Cristiaangz/Smart-Clamp/SmartClamp/ESP32/circuit schematic/v0.14.png

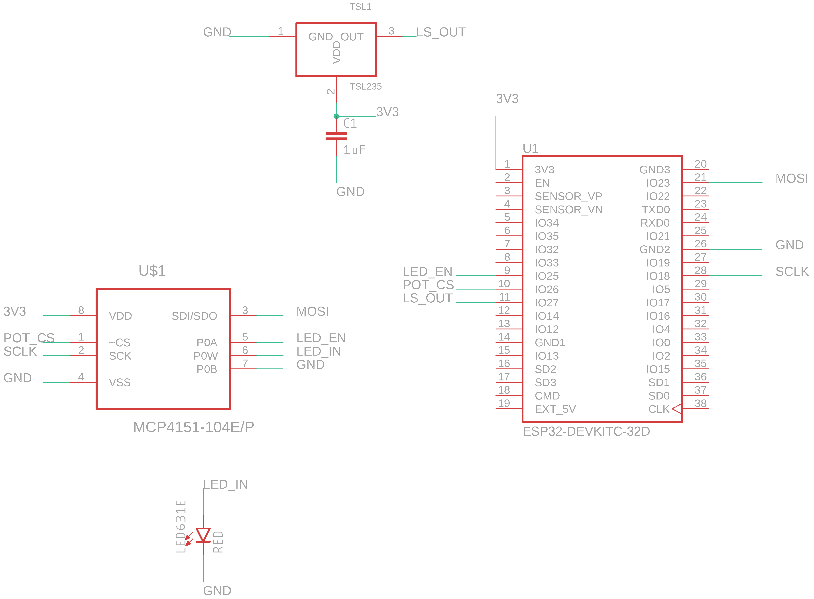
SmartClamp/ESP32/circuit schematic/v0.14.png
