Cristiaangz/Smart-Clamp/Tests/Initial Tests/Integrated Light and Motion Tests/30%Mid1.csv

Time [s] | Intensity A | Laser On | AcX | AcY | AcZ | GyX | GyY | GyZ | MPU Temp [C]
0.0 | 16.666666666666700 | TRUE | 0 | 0 | 0 | 0 | 0 | 0 | 25.352941176470600
0.10 | 500.0 | TRUE | 0 | 0 | 0 | 0 | 0 | 0 | 25.352941176470600
0.20 | 2200.0 | TRUE | 0 | 0 | 0 | 0 | 0 | 0 | 25.352941176470600
0.30 | 2200.0 | TRUE | 0 | 0 | 0 | 0 | 0 | 0 | 25.352941176470600
0.40 | 2183.3333333333300 | TRUE | 0 | 0 | 0 | 0 | 0 | 0 | 25.352941176470600
0.50 | 2200.0 | TRUE | 0 | 0 | 0 | 0 | 0 | 0 | 25.352941176470600
0.60 | 2200.0 | TRUE | 0 | 0 | 0 | 0 | 0 | 0 | 25.352941176470600
0.70 | 2183.3333333333300 | TRUE | 0 | 0 | 0 | 0 | 0 | 0 | 25.352941176470600
0.80 | 2200.0 | TRUE | 0 | 0 | 0 | 0 | 0 | 0 | 25.352941176470600
0.90 | 2200.0 | TRUE | 0 | 0 | 0 | 0 | 0 | 0 | 25.352941176470600
0.100 | 2200.0 | TRUE | 0 | 0 | 0 | 0 | 0 | 0 | 25.352941176470600
0.110 | 2183.3333333333300 | TRUE | 0 | 0 | 0 | 0 | 0 | 0 | 25.352941176470600
0.120 | 2200.0 | TRUE | 0 | 0 | 0 | 0 | 0 | 0 | 25.352941176470600
0.130 | 2200.0 | TRUE | 0 | 0 | 0 | 0 | 0 | 0 | 25.352941176470600
0.140 | 2183.3333333333300 | TRUE | 0 | 0 | 0 | 0 | 0 | 0 | 25.352941176470600
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
