Cristiaangz/Smart-Clamp/Tests/Initial Tests/Integrated Light and Motion Tests/30%Mid2.csv

Time [s] | Intensity A | Laser On | AcX | AcY | AcZ | GyX | GyY | GyZ | MPU Temp [C]
0.0 | 16.666666666666700 | TRUE | 0 | 0 | 0 | 0 | 0 | 0 | 25.541176470588200
0.10 | 433.3333333333330 | TRUE | 0 | 0 | 0 | 0 | 0 | 0 | 25.541176470588200
0.20 | 2183.3333333333300 | TRUE | 0 | 0 | 0 | 0 | 0 | 0 | 25.541176470588200
0.30 | 2200.0 | TRUE | 0 | 0 | 0 | 0 | 0 | 0 | 25.541176470588200
0.40 | 2183.3333333333300 | TRUE | 0 | 0 | 0 | 0 | 0 | 0 | 25.541176470588200
0.50 | 2200.0 | TRUE | 0 | 0 | 0 | 0 | 0 | 0 | 25.541176470588200
0.60 | 2200.0 | TRUE | 0 | 0 | 0 | 0 | 0 | 0 | 25.541176470588200
0.70 | 2183.3333333333300 | TRUE | 0 | 0 | 0 | 0 | 0 | 0 | 25.541176470588200
0.80 | 2200.0 | TRUE | 0 | 0 | 0 | 0 | 0 | 0 | 25.541176470588200
0.90 | 2200.0 | TRUE | 0 | 0 | 0 | 0 | 0 | 0 | 25.541176470588200
0.100 | 2183.3333333333300 | TRUE | 0 | 0 | 0 | 0 | 0 | 0 | 25.541176470588200
0.110 | 2200.0 | TRUE | 0 | 0 | 0 | 0 | 0 | 0 | 25.541176470588200
0.120 | 2183.3333333333300 | TRUE | 0 | 0 | 0 | 0 | 0 | 0 | 25.541176470588200
0.130 | 2200.0 | TRUE | 0 | 0 | 0 | 0 | 0 | 0 | 25.541176470588200
0.140 | 2200.0 | TRUE | 0 | 0 | 0 | 0 | 0 | 0 | 25.541176470588200
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
