Cristiaangz/Smart-Clamp/Tests/Initial Tests/Integrated Light and Motion Tests/30%Static1.csv

Time [s] | Intensity A | Laser On | AcX | AcY | AcZ | GyX | GyY | GyZ | MPU Temp [C]
0.0 | 16.666666666666700 | TRUE | 0 | 0 | 0 | 0 | 0 | 0 | 24.929411764705900
0.10 | 416.6666666666670 | TRUE | 0 | 0 | 0 | 0 | 0 | 0 | 24.929411764705900
0.20 | 2166.6666666666700 | TRUE | 0 | 0 | 0 | 0 | 0 | 0 | 24.929411764705900
0.30 | 2166.6666666666700 | TRUE | 0 | 0 | 0 | 0 | 0 | 0 | 24.929411764705900
0.40 | 2166.6666666666700 | TRUE | 0 | 0 | 0 | 0 | 0 | 0 | 24.929411764705900
0.50 | 2166.6666666666700 | TRUE | 0 | 0 | 0 | 0 | 0 | 0 | 24.929411764705900
0.60 | 2183.3333333333300 | TRUE | 0 | 0 | 0 | 0 | 0 | 0 | 24.929411764705900
0.70 | 2150.0 | TRUE | 0 | 0 | 0 | 0 | 0 | 0 | 24.929411764705900
0.80 | 2166.6666666666700 | TRUE | 0 | 0 | 0 | 0 | 0 | 0 | 24.929411764705900
0.90 | 2166.6666666666700 | TRUE | 0 | 0 | 0 | 0 | 0 | 0 | 24.929411764705900
0.100 | 2166.6666666666700 | TRUE | 0 | 0 | 0 | 0 | 0 | 0 | 24.929411764705900
0.110 | 2166.6666666666700 | TRUE | 0 | 0 | 0 | 0 | 0 | 0 | 24.929411764705900
0.120 | 2166.6666666666700 | TRUE | 0 | 0 | 0 | 0 | 0 | 0 | 24.929411764705900
0.130 | 2183.3333333333300 | TRUE | 0 | 0 | 0 | 0 | 0 | 0 | 24.929411764705900
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
