Cristiaangz/Smart-Clamp/Tests/Initial Tests/Integrated Light and Motion Tests/30%Static2.csv

Time [s] | Intensity A | Laser On | AcX | AcY | AcZ | GyX | GyY | GyZ | MPU Temp [C]
0.0 | 16.666666666666700 | TRUE | 0 | 0 | 0 | 0 | 0 | 0 | 25.16470588235290
0.10 | 666.6666666666670 | TRUE | 0 | 0 | 0 | 0 | 0 | 0 | 25.16470588235290
0.20 | 2166.6666666666700 | TRUE | 0 | 0 | 0 | 0 | 0 | 0 | 25.16470588235290
0.30 | 2183.3333333333300 | TRUE | 0 | 0 | 0 | 0 | 0 | 0 | 25.16470588235290
0.40 | 2150.0 | TRUE | 0 | 0 | 0 | 0 | 0 | 0 | 25.16470588235290
0.50 | 2183.3333333333300 | TRUE | 0 | 0 | 0 | 0 | 0 | 0 | 25.16470588235290
0.60 | 2166.6666666666700 | TRUE | 0 | 0 | 0 | 0 | 0 | 0 | 25.16470588235290
0.70 | 2166.6666666666700 | TRUE | 0 | 0 | 0 | 0 | 0 | 0 | 25.16470588235290
0.80 | 2166.6666666666700 | TRUE | 0 | 0 | 0 | 0 | 0 | 0 | 25.16470588235290
0.90 | 2166.6666666666700 | TRUE | 0 | 0 | 0 | 0 | 0 | 0 | 25.16470588235290
0.100 | 2183.3333333333300 | TRUE | 0 | 0 | 0 | 0 | 0 | 0 | 25.16470588235290
0.110 | 2166.6666666666700 | TRUE | 0 | 0 | 0 | 0 | 0 | 0 | 25.16470588235290
0.120 | 2166.6666666666700 | TRUE | 0 | 0 | 0 | 0 | 0 | 0 | 25.16470588235290
0.130 | 2166.6666666666700 | TRUE | 0 | 0 | 0 | 0 | 0 | 0 | 25.16470588235290
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
