Cristiaangz/Smart-Clamp/Tests/Initial Tests/Gyro/Rotation Tests/10Hz/Graphs/28 RPM/AcX 28 RPM.png

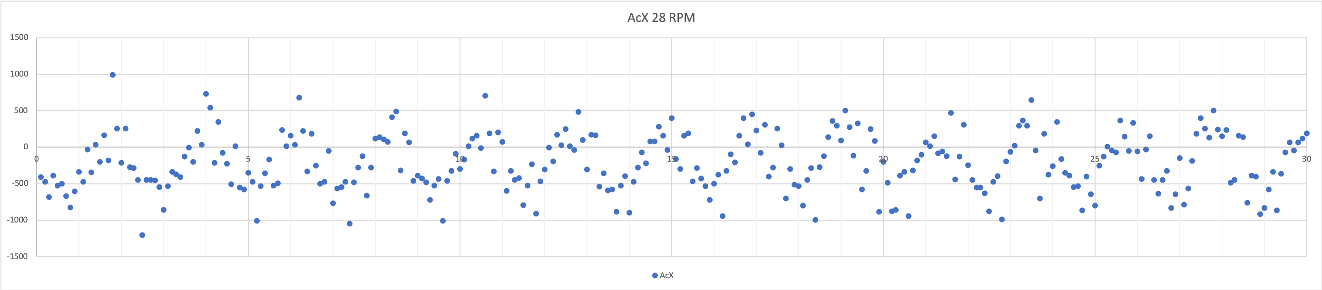
Tests/Initial Tests/Gyro/Rotation Tests/10Hz/Graphs/28 RPM/AcX 28 RPM.png
