Cristiaangz/Smart-Clamp/Tests/Initial Tests/Gyro/Rotation Tests/10Hz/Graphs/28 RPM/AcY 28 RPM.png

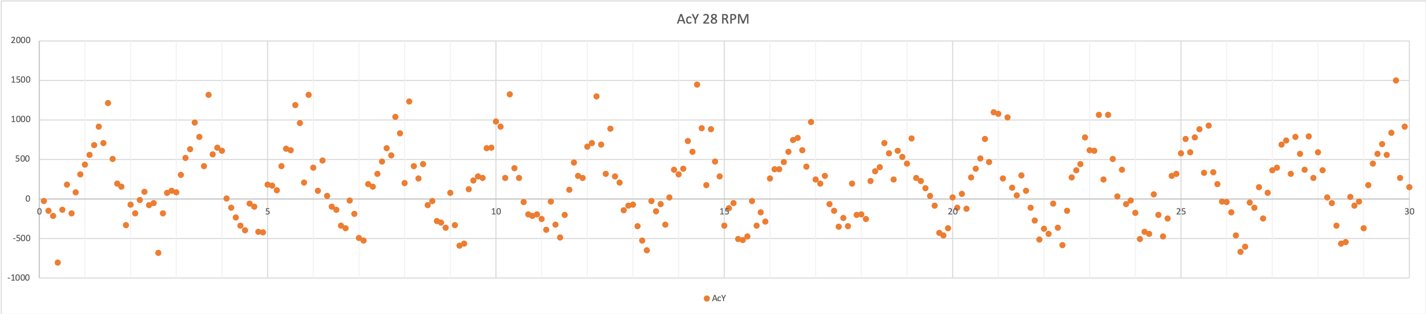
Tests/Initial Tests/Gyro/Rotation Tests/10Hz/Graphs/28 RPM/AcY 28 RPM.png
