Cristiaangz/Smart-Clamp/Tests/Initial Tests/Gyro/Rotation Tests/10Hz/Graphs/80 RPM.png

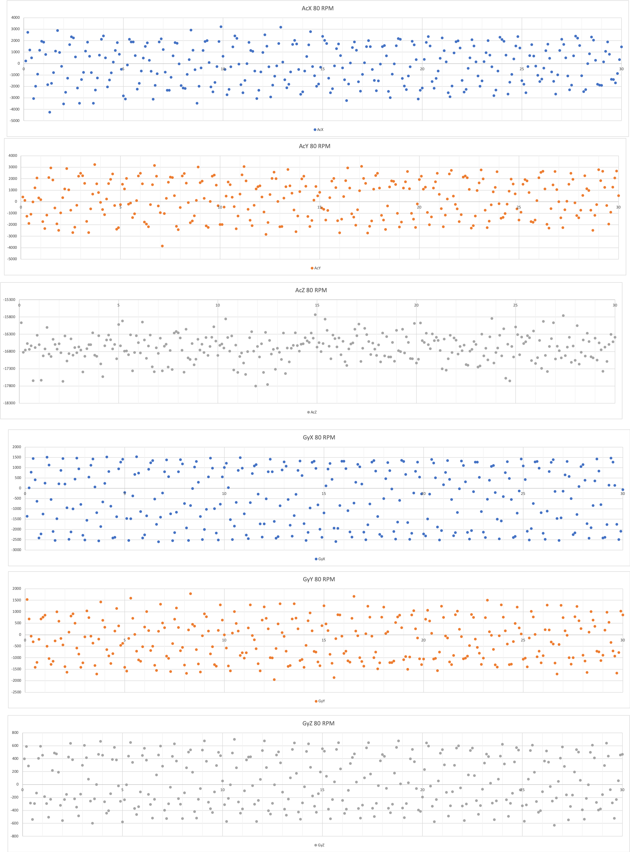
Tests/Initial Tests/Gyro/Rotation Tests/10Hz/Graphs/80 RPM.png
