Cristiaangz/Smart-Clamp/Tests/Initial Tests/Gyro/Rotation Tests/10Hz/Graphs/Static.png/Static.png-2.png

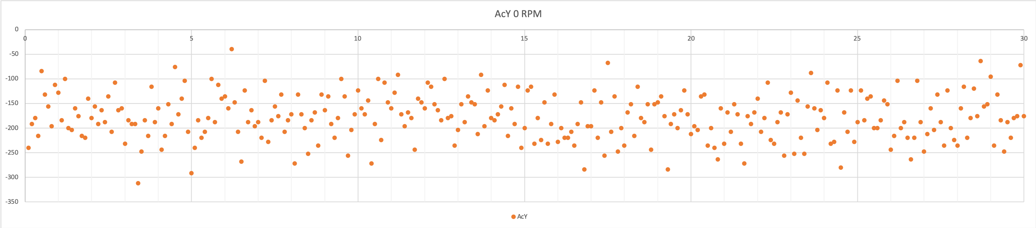
Tests/Initial Tests/Gyro/Rotation Tests/10Hz/Graphs/Static.png/Static.png-2.png
