Cristiaangz/Smart-Clamp/Tests/Initial Tests/Gyro/Rotation Tests/100 Hz/Graphs/30 Hz 11:06:19.png/30 Hz 11:06:19.png-5.png

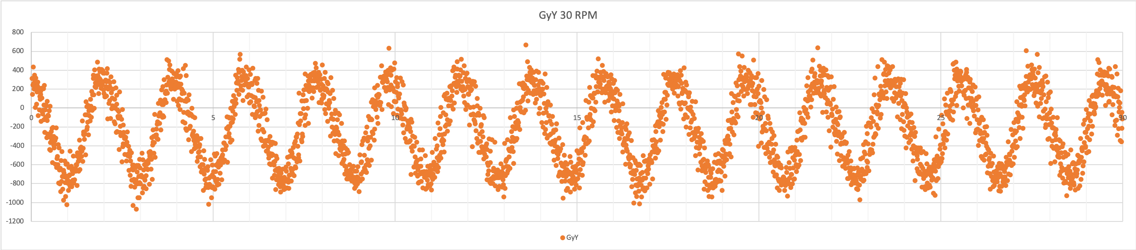
Tests/Initial Tests/Gyro/Rotation Tests/100 Hz/Graphs/30 Hz 11:06:19.png/30 Hz 11:06:19.png-5.png
