Cristiaangz/Smart-Clamp/Tests/Initial Tests/OD/Apple Juice June 24/0%AJ1.png

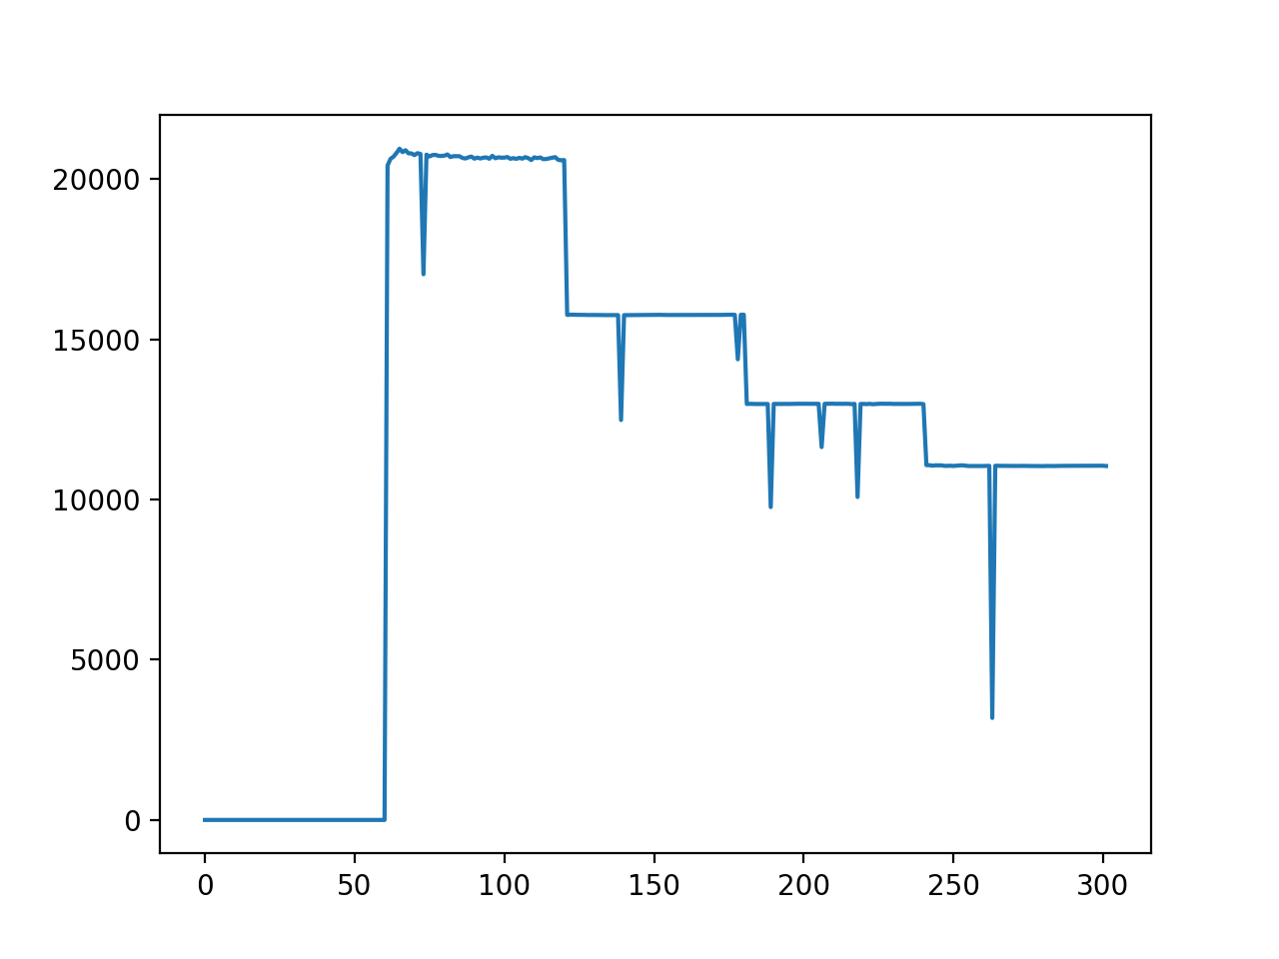
Tests/Initial Tests/OD/Apple Juice June 24/0%AJ1.png
