Cristiaangz/Smart-Clamp/Tests/Initial Tests/OD/Apple Juice June 24/10%AJ1.png

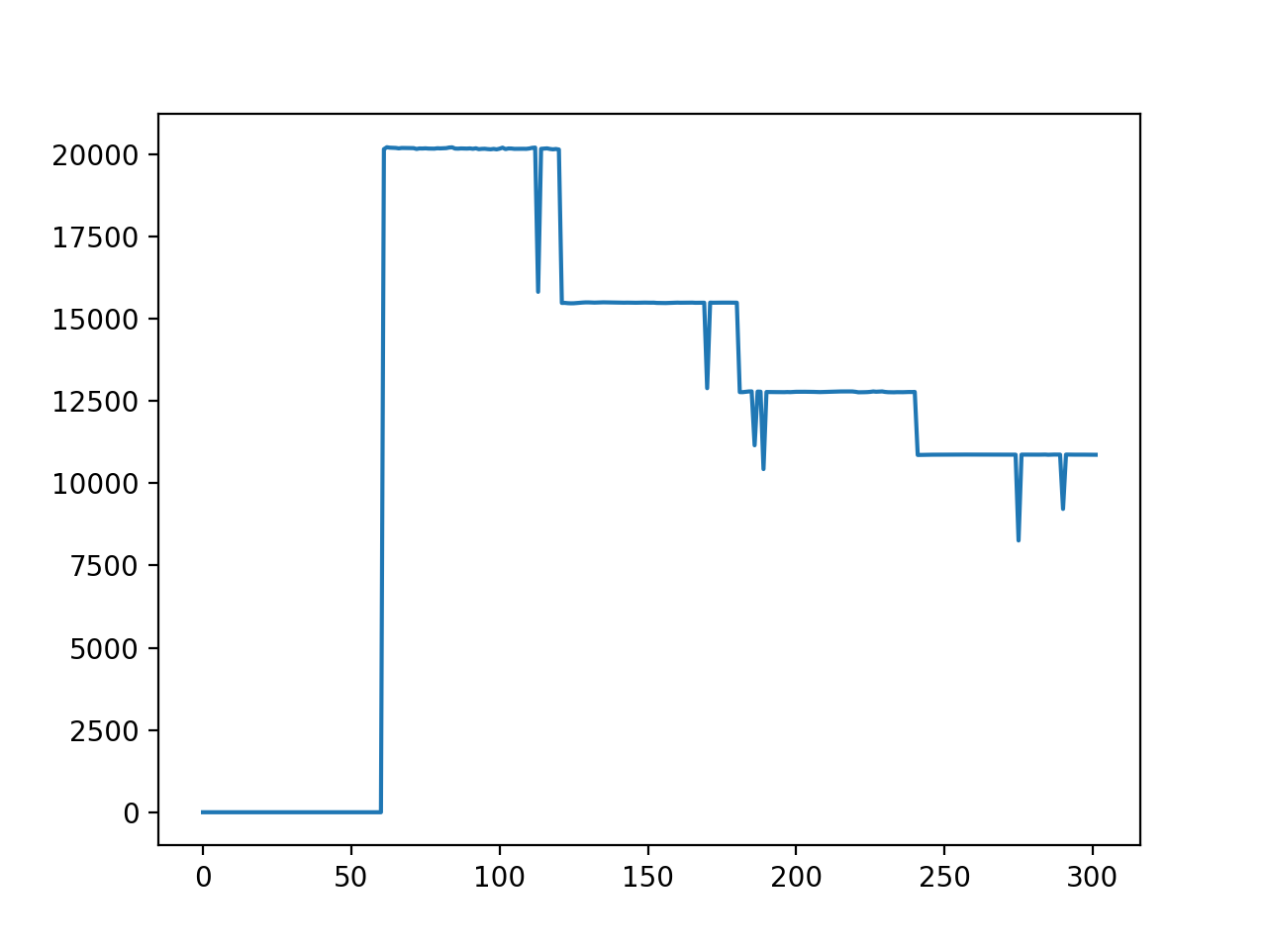
Tests/Initial Tests/OD/Apple Juice June 24/10%AJ1.png
