Cristiaangz/Smart-Clamp/Tests/Initial Tests/OD/Apple Juice June 24/50%AJ2.png

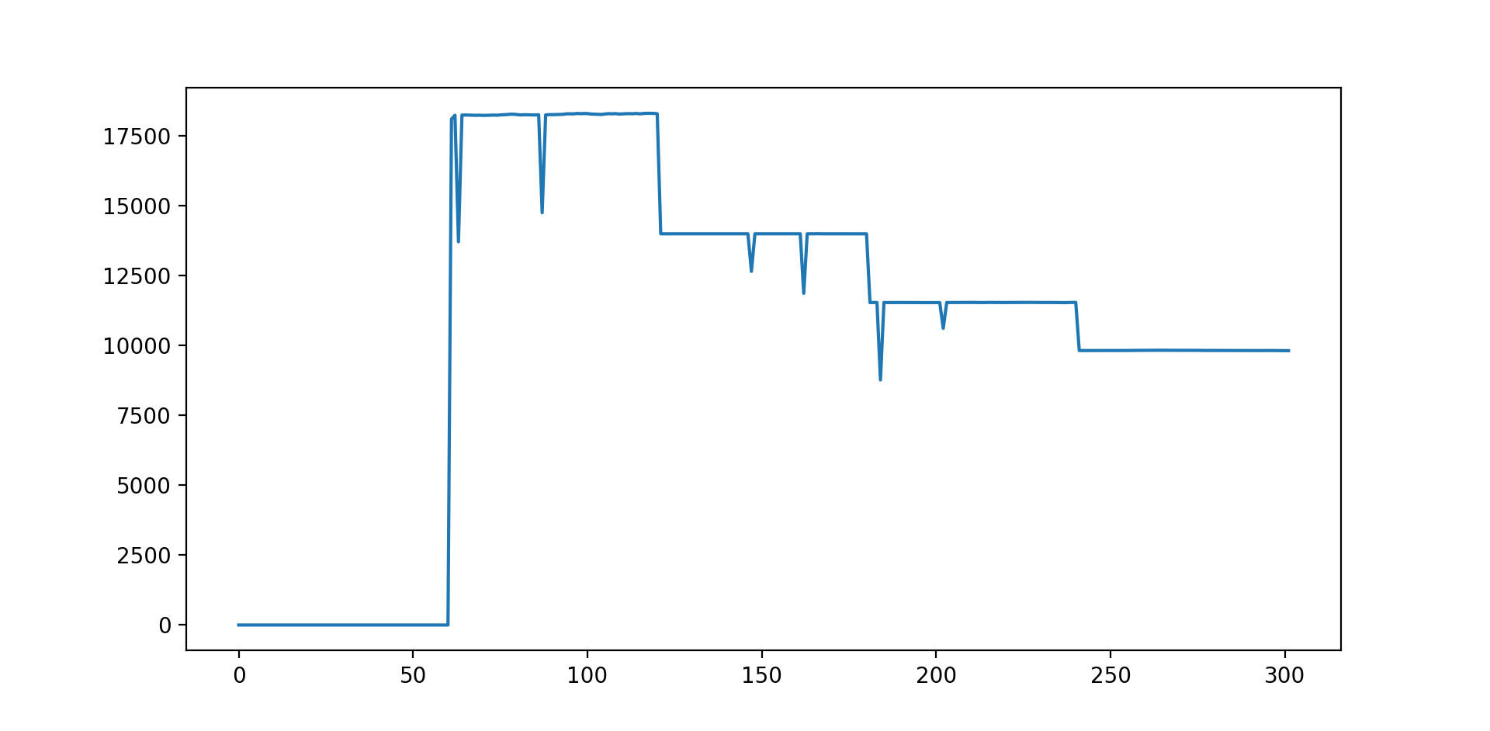
Tests/Initial Tests/OD/Apple Juice June 24/50%AJ2.png
