Cristiaangz/Smart-Clamp/Tests/Initial Tests/OD/Apple Juice June 24/128.png

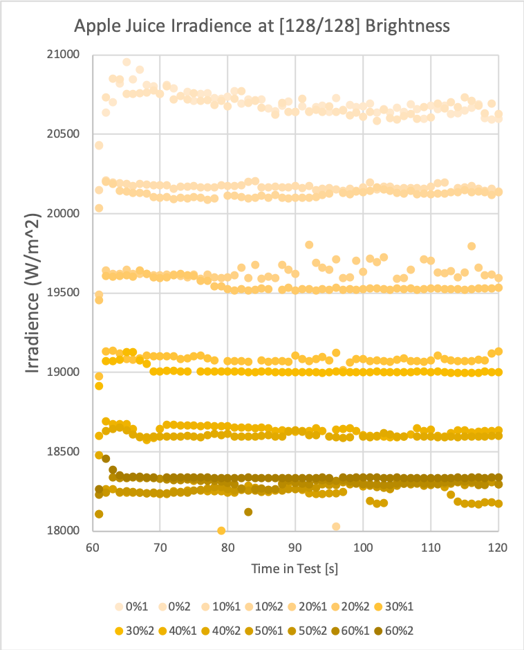
Tests/Initial Tests/OD/Apple Juice June 24/128.png
