Cristiaangz/Smart-Clamp/Tests/Initial Tests/OD/Light Detection June 23 2019/Filtered Ambien light + red LED.png

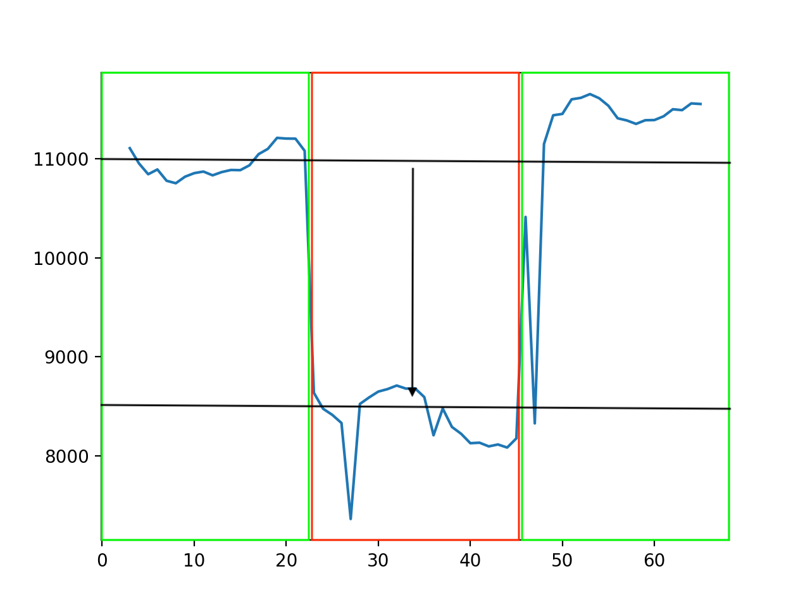
Tests/Initial Tests/OD/Light Detection June 23 2019/Filtered Ambien light + red LED.png
