Cristiaangz/Smart-Clamp/Tests/Initial Tests/OD/Light Detection June 23 2019/Unfiltered Ambient Light.png

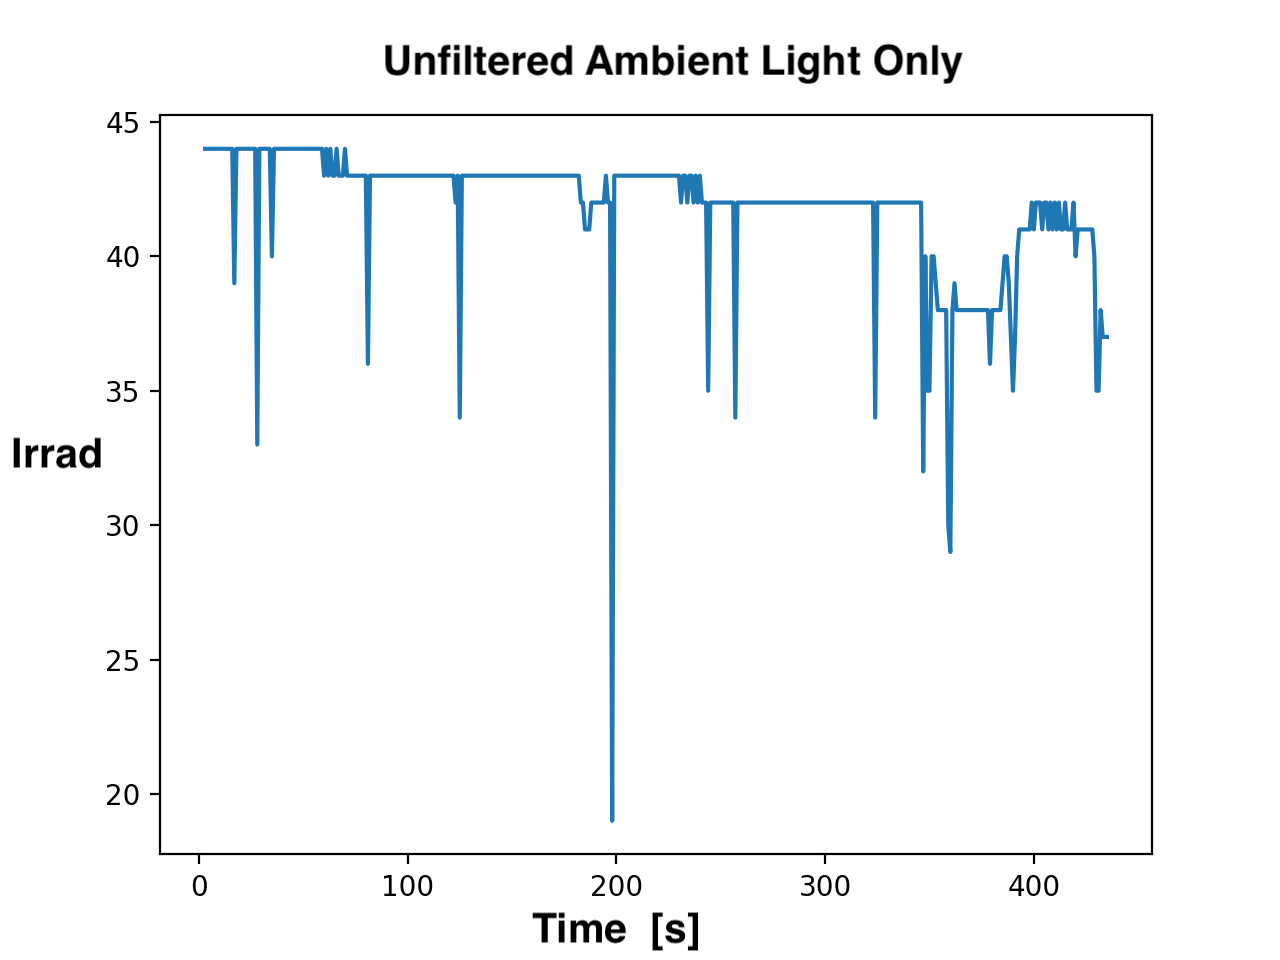
Tests/Initial Tests/OD/Light Detection June 23 2019/Unfiltered Ambient Light.png
