Cristiaangz/Smart-Clamp/Tests/Initial Tests/OD/Medium + Cells Test/1_21.png

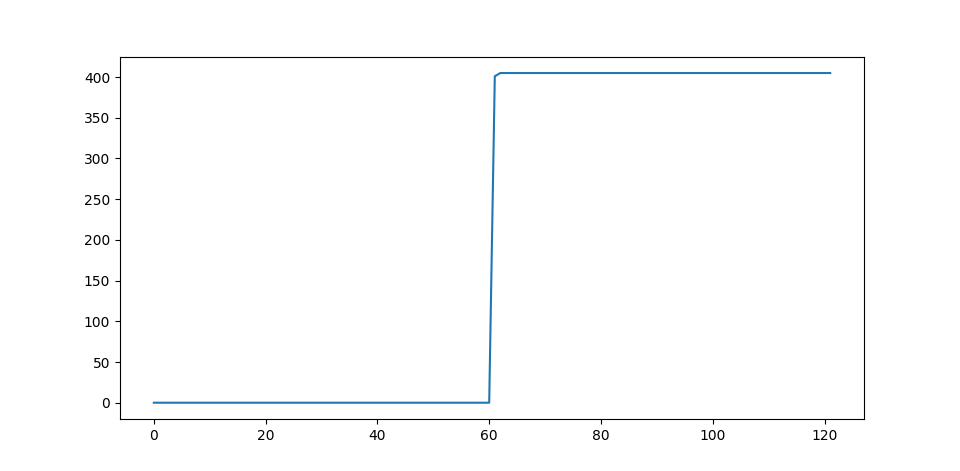
Tests/Initial Tests/OD/Medium + Cells Test/1_21.png
