Cristiaangz/Smart-Clamp/Tests/Initial Tests/OD/Medium + Cells Test/1_23.png

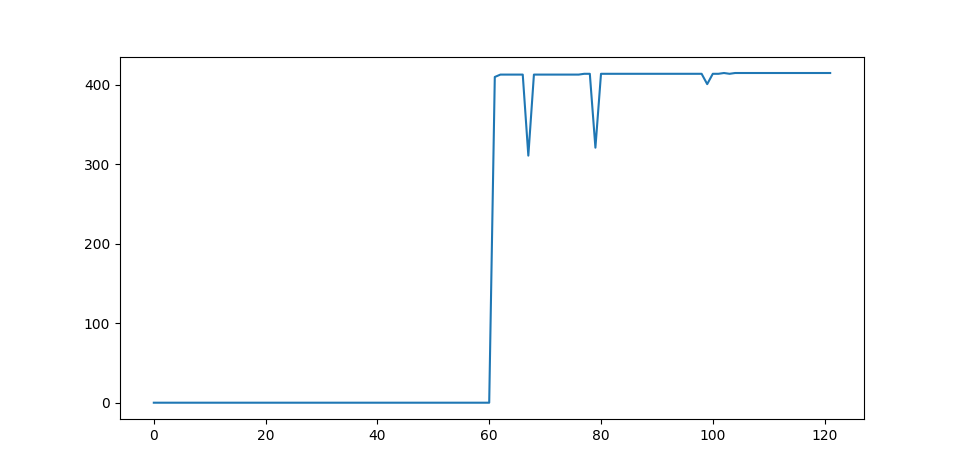
Tests/Initial Tests/OD/Medium + Cells Test/1_23.png
