Cristiaangz/Smart-Clamp/Tests/Initial Tests/OD/Medium + Cells Test/1_128_1.png

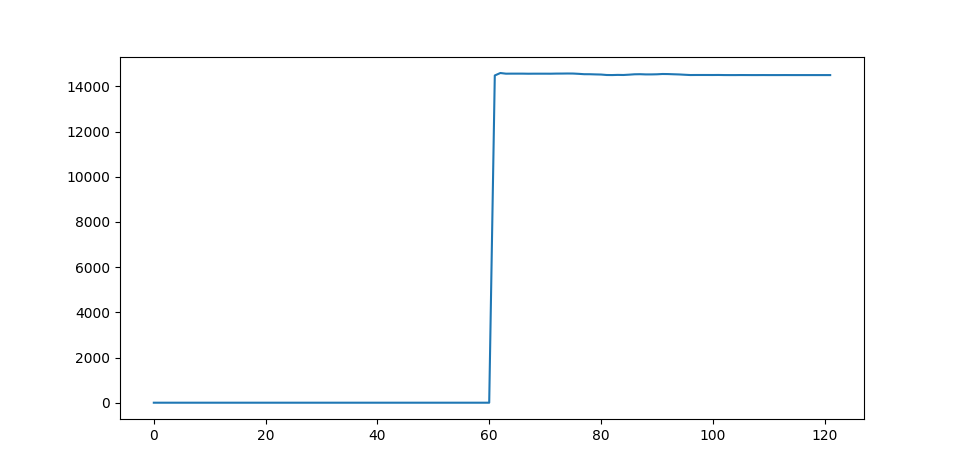
Tests/Initial Tests/OD/Medium + Cells Test/1_128_1.png
