Cristiaangz/Smart-Clamp/Tests/Initial Tests/OD/Medium + Cells Test/mediumOnly1.png

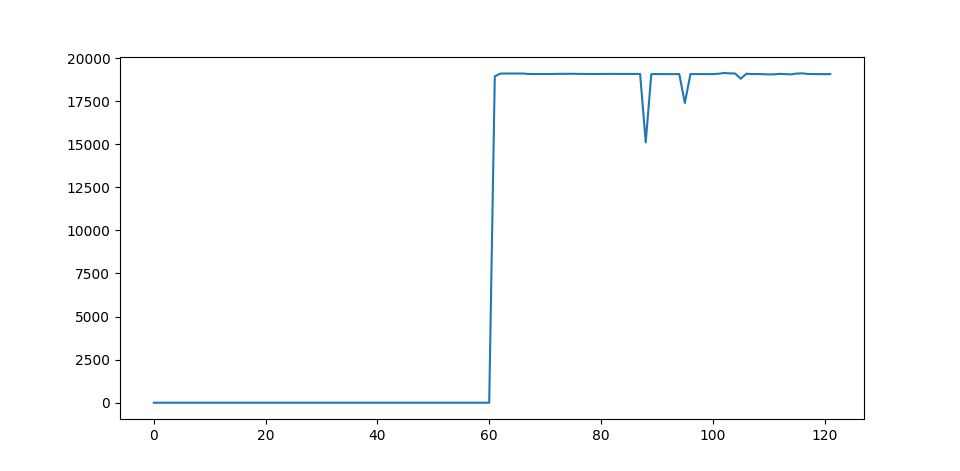
Tests/Initial Tests/OD/Medium + Cells Test/mediumOnly1.png
