Cristiaangz/Smart-Clamp/Scientific Papers/Hoffman Source Files/journal.pone.0181923.s001.png

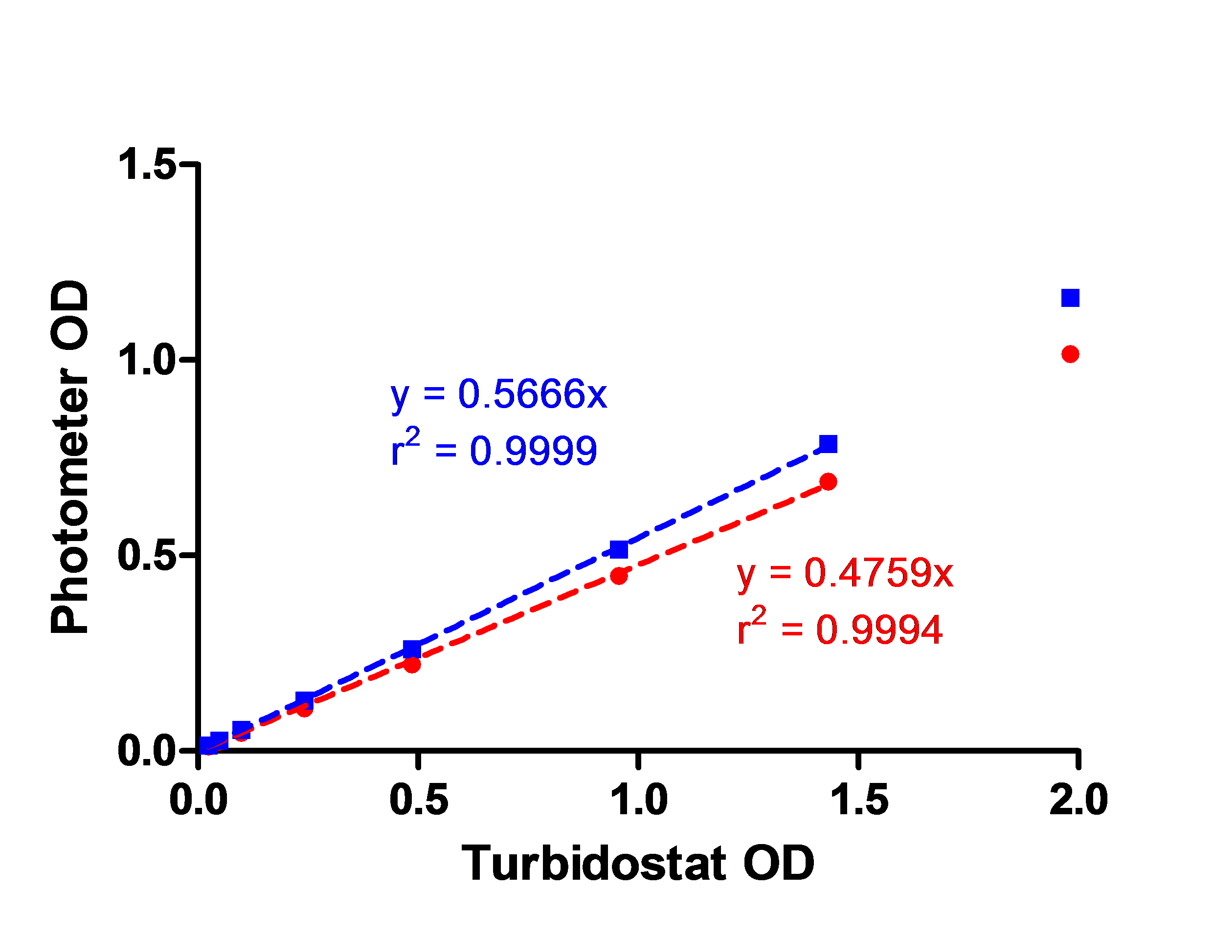
Scientific Papers/Hoffman Source Files/journal.pone.0181923.s001.png
