Cristiaangz/Smart-Clamp/SmartClamp/ESP32/circuit schematic/smartclamp v0.14.sch

## EAGLE design SmartClamp/ESP32/circuit schematic/smartclamp v0.14.sch (2019-09-08)

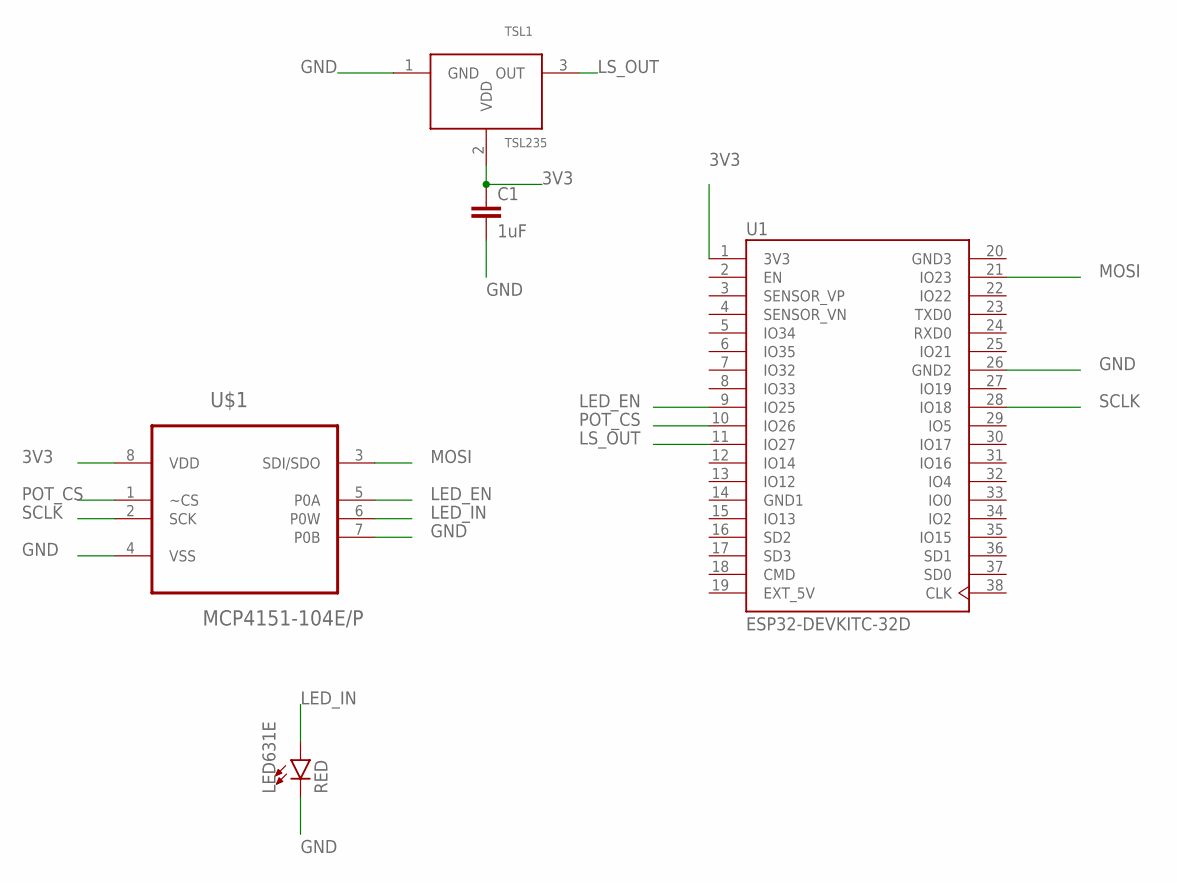
[picture p49: schematic smartclamp v0.14.sch]

Parts:
C1: 1uF; 0603
LED631E: RED; LED-1206
TSL1: TSL235; TSL235-P
U1: ESP32-DEVKITC-32D; MODULE_ESP32-DEVKITC-32D
U$1: MCP4151-104E/P; DIP254P762X533-8

Connections:
3V3: C1.1, TSL1.2 (VDD), U1.1 (3V3), U$1.8 (VDD)
GND: C1.2, LED631E.C, TSL1.1 (GND), U1.26 (GND2), U$1.4 (VSS), U$1.7 (P0B)
LED_EN: U1.9 (IO25), U$1.5 (P0A)
LED_IN: LED631E.A, U$1.6 (P0W)
LS_OUT: TSL1.3 (OUT), U1.11 (IO27)
MOSI: U1.21 (IO23), U$1.3 (SDI/SDO)
POT_CS: U1.10 (IO26), U$1.1 (~CS)
SCLK: U1.28 (IO18), U$1.2 (SCK)
