Cristiaangz/Smart-Clamp/Sample Code/MPU-6050_IMU/MPU-6050_IMU.ino

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

///////////////////////////////////////////////////////////////////////////////////////
//Support
///////////////////////////////////////////////////////////////////////////////////////
Website: http://www.brokking.net/imu.html
Youtube: https://youtu.be/4BoIE8YQwM8
Version: 1.0 (May 5, 2016)

///////////////////////////////////////////////////////////////////////////////////////
//Connections
///////////////////////////////////////////////////////////////////////////////////////
Power (5V) is provided to the Arduino pro mini by the FTDI programmer

Gyro - Arduino pro mini
VCC  -  5V
GND  -  GND
SDA  -  A4
SCL  -  A5

LCD  - Arduino pro mini
VCC  -  5V
GND  -  GND
SDA  -  A4
SCL  -  A5
*//////////////////////////////////////////////////////////////////////////////////////

//Include LCD and I2C library

#include <Wire.h>

//Declaring some global variables
int raw_gyro_x, raw_gyro_y, raw_gyro_z;
long acc_x, acc_y, acc_z, acc_total_vector;
int temperature;
long gyro_x_cal, gyro_y_cal, gyro_z_cal;
long loop_timer;
int lcd_loop_counter;
float gyro, angle_roll;
int angle_pitch_buffer, angle_roll_buffer;
boolean set_gyro_angles;
float angle_roll_acc, angle_pitch_acc;
float angle_pitch_output, angle_roll_output;


void setup() {
  Wire.begin();                                                        //Start I2C as master
  Serial.begin(57600);                                               //Use only for debugging
  pinMode(13, OUTPUT);                                                 //Set output 13 (LED) as output
  
  setup_mpu_6050_registers();                                          //Setup the registers of the MPU-6050 (500dfs / +/-8g) and start the gyro

  digitalWrite(13, HIGH);                                              //Set digital output 13 high to indicate startup
  
  Serial.println("Calibrating gyro"); 
  
  for (int cal_int = 0; cal_int < 2000 ; cal_int ++){                  //Run this code 2000 times
    read_mpu_6050_data();                                              //Read the raw acc and gyro data from the MPU-6050
    gyro_x_cal += raw_gyro_x;                                              //Add the gyro x-axis offset to the gyro_x_cal variable
    gyro_y_cal += raw_gyro_y;                                              //Add the gyro y-axis offset to the gyro_y_cal variable
    gyro_z_cal += raw_gyro_z;                                              //Add the gyro z-axis offset to the gyro_z_cal variable
    delay(3);                                                          //Delay 3us to simulate the 250Hz program loop
  }
  gyro_x_cal /= 2000;                                                  //Divide the gyro_x_cal variable by 2000 to get the average offset
  gyro_y_cal /= 2000;                                                  //Divide the gyro_y_cal variable by 2000 to get the average offset
  gyro_z_cal /= 2000;                                                  //Divide the gyro_z_cal variable by 2000 to get the average offset
  
  digitalWrite(13, LOW);                                               //All done, turn the LED off
  
  loop_timer = micros();                                               //Reset the loop timer
}

void loop(){

  read_mpu_6050_data();                                                //Read the raw acc and gyro data from the MPU-6050

  raw_gyro_x -= gyro_x_cal;                                                //Subtract the offset calibration value from the raw_gyro_x value
  raw_gyro_y -= gyro_y_cal;                                                //Subtract the offset calibration value from the raw_gyro_yvalue
  raw_gyro_z-= gyro_z_cal;                                                //Subtract the offset calibration value from the raw_gyro_zvalue
  
  //Gyro angle calculations
  //0.0000611 = 1 / (250Hz / 65.5)
  gyro_x += raw_gyro_x * 0.0000611;                                   //Calculate the traveled pitch angle and add this to the angle_pitch variable
  gyro_y += raw_gyro_y* 0.0000611;                                    //Calculate the traveled roll angle and add this to the angle_roll variable
  
  //0.000001066 = 0.0000611 * (3.142(PI) / 180degr) The Arduino sin function is in radians
  //angle_pitch += angle_roll * sin(raw_gyro_z * 0.000001066);               //If the IMU has yawed transfer the roll angle to the pitch angel
  //angle_roll -= angle_pitch * sin(raw_gyro_z * 0.000001066);               //If the IMU has yawed transfer the pitch angle to the roll angel
  
  //Accelerometer angle calculations
  acc_total_vector = sqrt((acc_x*acc_x)+(acc_y*acc_y)+(acc_z*acc_z));  //Calculate the total accelerometer vector
  //57.296 = 1 / (3.142 / 180) The Arduino asin function is in radians
  angle_pitch_acc = asin((float)acc_y/acc_total_vector)* 57.296;       //Calculate the pitch angle
  angle_roll_acc = asin((float)acc_x/acc_total_vector)* -57.296;       //Calculate the roll angle
  
  //Place the MPU-6050 spirit level and note the values in the following two lines for calibration
  angle_pitch_acc -= 0.0;                                              //Accelerometer calibration value for pitch
  angle_roll_acc -= 0.0;                                               //Accelerometer calibration value for roll

  if(set_gyro_angles){                                                 //If the IMU is already started
    angle_pitch = angle_pitch * 0.9996 + angle_pitch_acc * 0.0004;     //Correct the drift of the gyro pitch angle with the accelerometer pitch angle
    angle_roll = angle_roll * 0.9996 + angle_roll_acc * 0.0004;        //Correct the drift of the gyro roll angle with the accelerometer roll angle
  }
  else{                                                                //At first start
    angle_pitch = angle_pitch_acc;                                     //Set the gyro pitch angle equal to the accelerometer pitch angle 
    angle_roll = angle_roll_acc;                                       //Set the gyro roll angle equal to the accelerometer roll angle 
    set_gyro_angles = true;                                            //Set the IMU started flag
  }
  
  //To dampen the pitch and roll angles a complementary filter is used
  angle_pitch_output = angle_pitch_output * 0.9 + angle_pitch * 0.1;   //Take 90% of the output pitch value and add 10% of the raw pitch value
  angle_roll_output = angle_roll_output * 0.9 + angle_roll * 0.1;      //Take 90% of the output roll value and add 10% of the raw roll value
  
  //write_LCD();                                                         //Write the roll and pitch values to the LCD display
  write_SERIAL();

  while(micros() - loop_timer < 4000);                                 //Wait until the loop_timer reaches 4000us (250Hz) before starting the next loop
  loop_timer = micros();                                               //Reset the loop timer
}


void read_mpu_6050_data(){                                             //Subroutine for reading the raw gyro and accelerometer data
  Wire.beginTransmission(0x68);                                        //Start communicating with the MPU-6050
  Wire.write(0x3B);                                                    //Send the requested starting register
  Wire.endTransmission();                                              //End the transmission
  Wire.requestFrom(0x68,14);                                           //Request 14 bytes from the MPU-6050
  while(Wire.available() < 14);                                        //Wait until all the bytes are received
  acc_x = Wire.read()<<8|Wire.read();                                  //Add the low and high byte to the acc_x variable
  acc_y = Wire.read()<<8|Wire.read();                                  //Add the low and high byte to the acc_y variable
  acc_z = Wire.read()<<8|Wire.read();                                  //Add the low and high byte to the acc_z variable
  temperature = Wire.read()<<8|Wire.read();                            //Add the low and high byte to the temperature variable
  raw_gyro_x = Wire.read()<<8|Wire.read();                                 //Add the low and high byte to the raw_gyro_x variable
  raw_gyro_y= Wire.read()<<8|Wire.read();                                 //Add the low and high byte to the raw_gyro_yvariable
  raw_gyro_z= Wire.read()<<8|Wire.read();                                 //Add the low and high byte to the raw_gyro_zvariable

}

void write_SERIAL(){                                                      //Subroutine for writing the LCD
  //To get a 250Hz program loop (4us) it's only possible to write one character per loop
  //Writing multiple characters is taking to much time
  Serial.print("\t");
  Serial.print(angle_pitch_output);    //Print Pitch number
  Serial.print("\t");
  Serial.println(angle_roll_output);    //Print Roll number
}


void setup_mpu_6050_registers(){
  //Activate the MPU-6050
  Wire.beginTransmission(0x68);                                        //Start communicating with the MPU-6050
  Wire.write(0x6B);                                                    //Send the requested starting register
  Wire.write(0x00);                                                    //Set the requested starting register
  Wire.endTransmission();                                              //End the transmission
  //Configure the accelerometer (+/-8g)
  Wire.beginTransmission(0x68);                                        //Start communicating with the MPU-6050
  Wire.write(0x1C);                                                    //Send the requested starting register
  Wire.write(0x10);                                                    //Set the requested starting register
  Wire.endTransmission();                                              //End the transmission
  //Configure the gyro (500dps full scale)
  Wire.beginTransmission(0x68);                                        //Start communicating with the MPU-6050
  Wire.write(0x1B);                                                    //Send the requested starting register
  Wire.write(0x08);                                                    //Set the requested starting register
  Wire.endTransmission();                                              //End the transmission
}
