Cristiaangz/Smart-Clamp/Sample Code/MCP4131/MCP4131.ino

#include <SPI.h>

byte address = 0x00;
int CS= 10;

void setup()
{
pinMode (CS, OUTPUT);
SPI.begin();
}

void loop()
{
for (int i = 0; i <= 128; i++)
{
digitalPotWrite(i);
delay(10);
}
delay(5000);
for (int i = 128; i >= 0; i--)
{
digitalPotWrite(i);
delay(10);
}
}

int digitalPotWrite(int value)
{
digitalWrite(CS, LOW);
SPI.transfer(address);
SPI.transfer(value);
digitalWrite(CS, HIGH);
}
